ltspicer/Thyristor-Triac-Tester/aufbau1.jpg

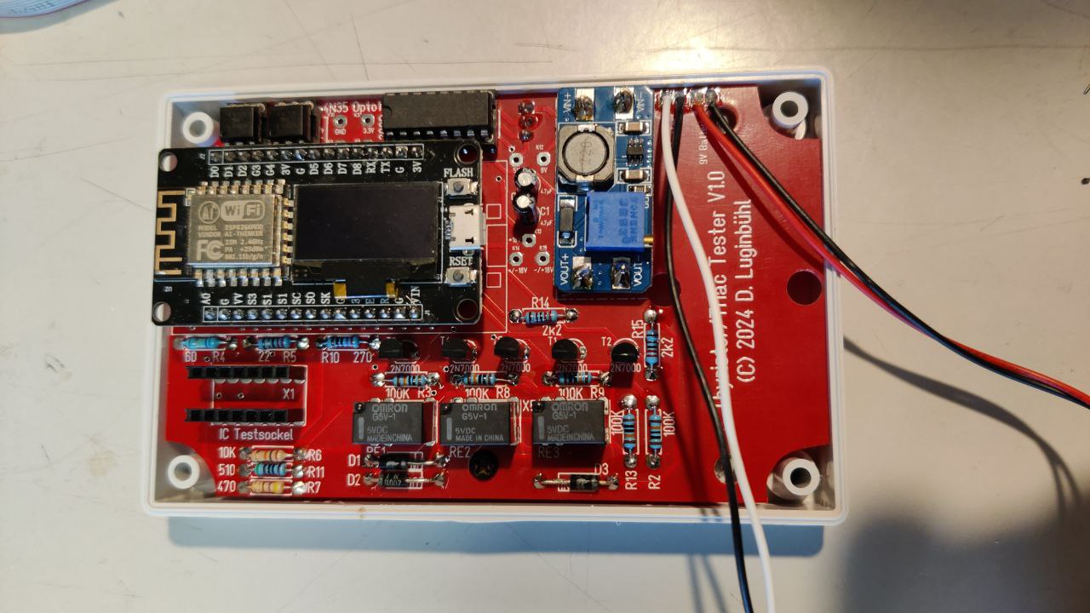
aufbau1.jpg
