ltspicer/Thyristor-Triac-Tester/esp_test.jpg

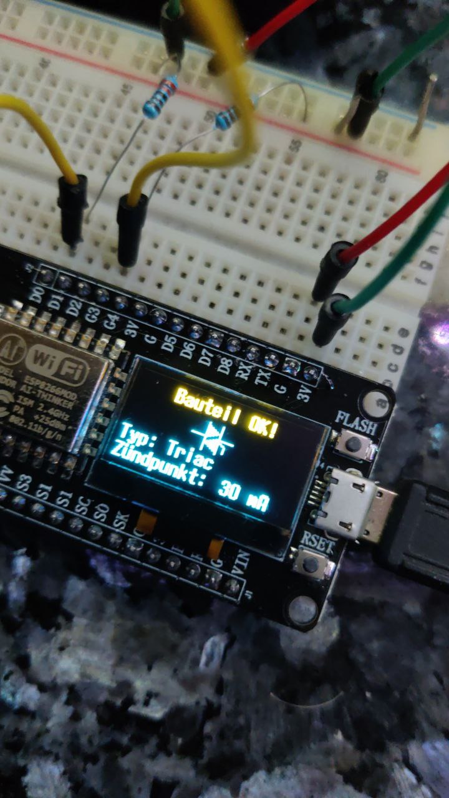
esp_test.jpg
